aguscsc/Bidirectional-Buck-DC-DC-converter/pics/BOOST_V.PNG

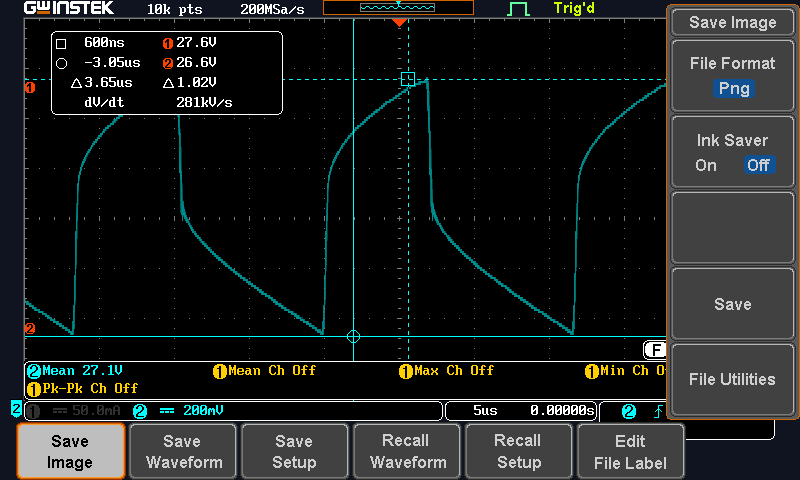
pics/BOOST_V.PNG
