aguscsc/Bidirectional-Buck-DC-DC-converter/Design/Simulations/ltspice/synchronus_boost.asc

C1: cap; 6.8µ; V=4 Irms=9.59 Rser=0.00574865 Lser=0 mfg="KEMET" pn="C0603C685K7PAC" type="X5R"
C2: cap; 2.2µ; V=4 Irms=7.1 Rser=0.00682 Lser=0 mfg="KEMET" pn="C0805C225K7PAC" type="X5R"
C3: cap; 0.1µ; V=4 Irms=0 Rser=0 Lser=0 mfg="Murata" pn="GRM022R60G153KE15" type="X5R"
C4: cap; 0.1µ; V=4 Irms=0 Rser=0 Lser=0 mfg="Murata" pn="GRM022R60G153KE15" type="X5R"
D2: diode; SS24
L1: ind; 1m; Rser=0.3
M1: nmos; IRFZ44N
M2: nmos; IRFZ44N
R1: res; 145
R2: res; 10
R3: res; 10
R4: res; 10k
R5: res; 10k
U2: IR2184
V1: voltage; 12
V2: voltage; 12v
V3: voltage; PULSE(0 5 0 20n 20n 7.5u 16.66u)
Named nets: 0, hi_buck, LO_buck, VS_buck
.include Z:\\home\\wepi\\circuits\\synchronus_buck\\irfz44n.spi
.include Z:\\home\\wepi\\circuits\\synchronus_buck\\IR2184.sub
.tran 0 0.1 0
BUCK
